drkntz/Dimmer/Software/Settings.py

# Settings.py: This is the settings module for the Dimmer script. It contains the speed profile that is chosen
# and other settings to come later if necessary.
# Created 11 Aug 2020 by Zach Martin

##### Dimmer Profile. This is the setting for the ramping up of the output voltage. 
# Manual = 0, Custom Motor = 1, Full Range = 2, Custom Light = 3
dimmerProfile = 1
